J1234D/ByteBoard/assets/Renderings/untitled.199.jpg

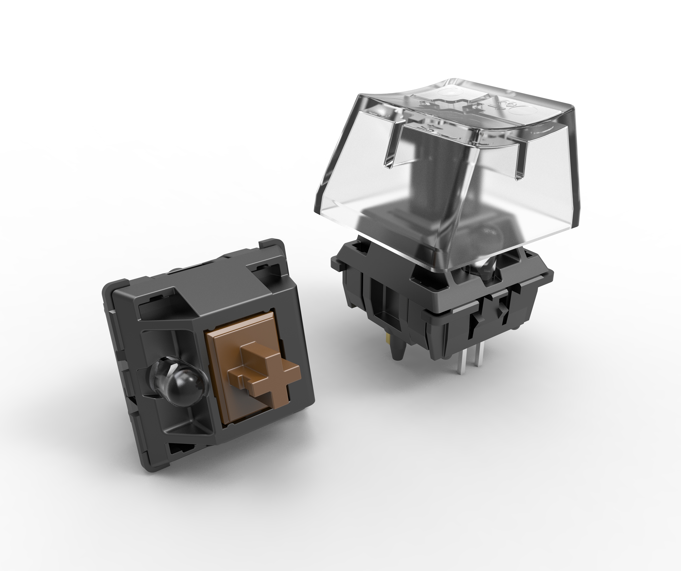
assets/Renderings/untitled.199.jpg
