J1234D/ByteBoard/assets/Renderings/屏幕截图(22).jpg

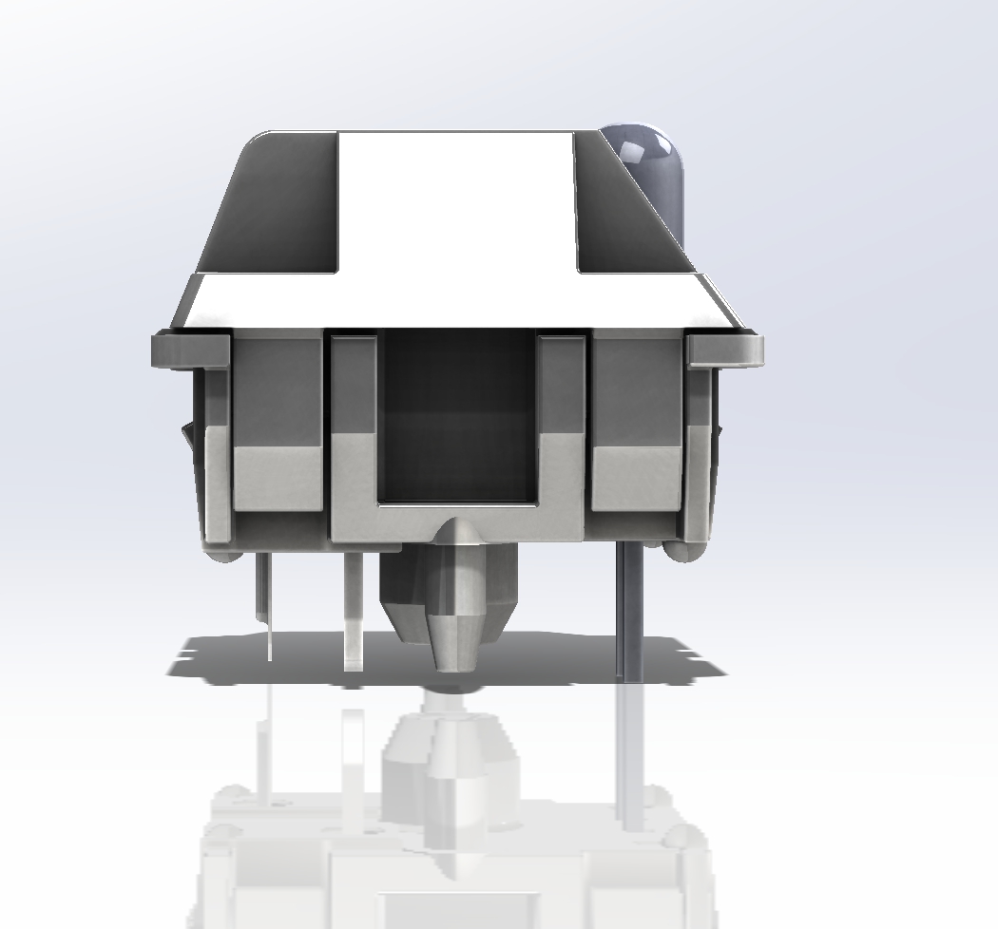
assets/Renderings/屏幕截图(22).jpg
