J1234D/ByteBoard/assets/Renderings/屏幕截图(25).jpg

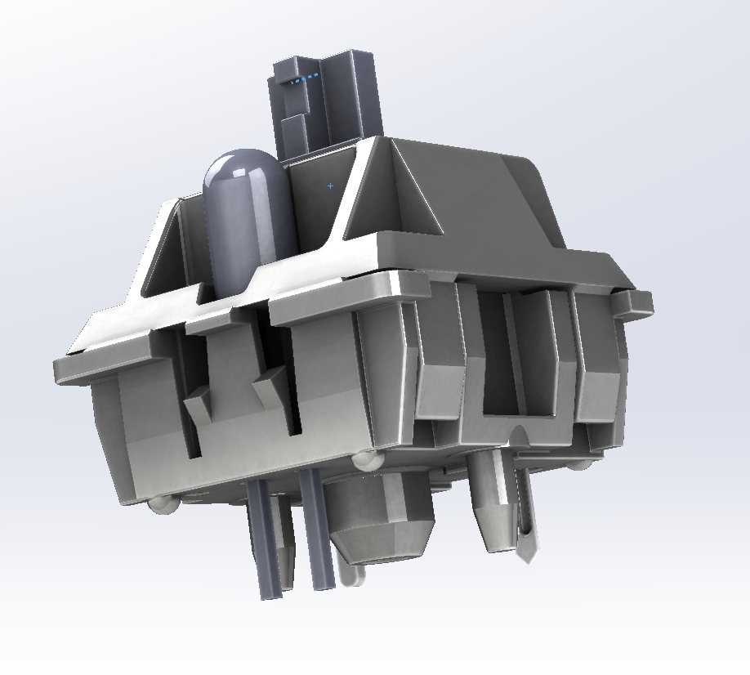
assets/Renderings/屏幕截图(25).jpg
