J1234D/ByteBoard/assets/Renderings/屏幕截图(26).jpg

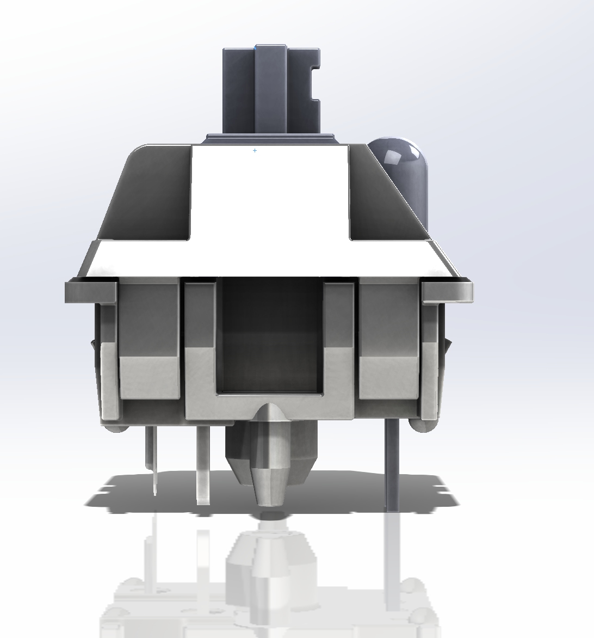
assets/Renderings/屏幕截图(26).jpg
