J1234D/ByteBoard/assets/Renderings/屏幕截图(27)_副本.jpg

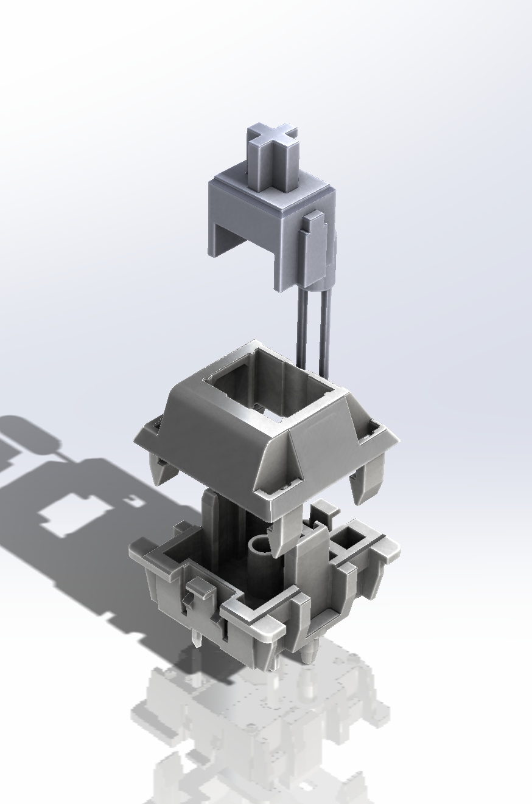
assets/Renderings/屏幕截图(27)_副本.jpg
