J1234D/ByteBoard/assets/Rotary_encoder/1.PNG

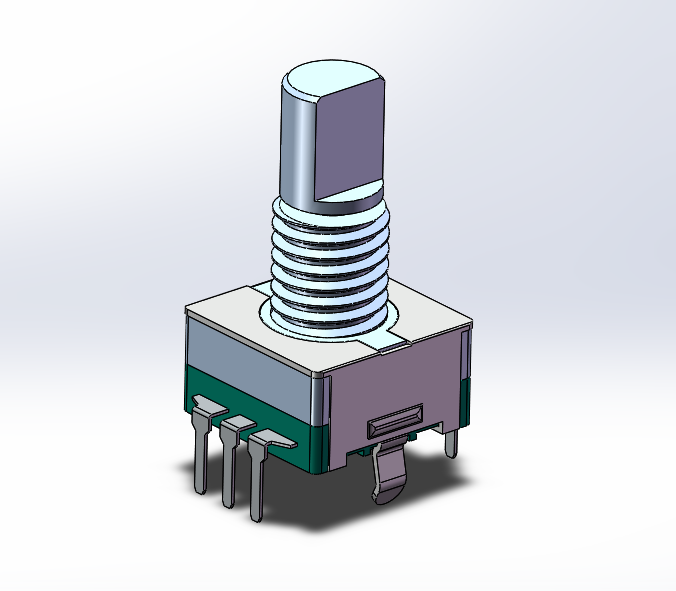
assets/Rotary_encoder/1.PNG
