J1234D/ByteBoard/assets/Rotary_encoder/2.PNG

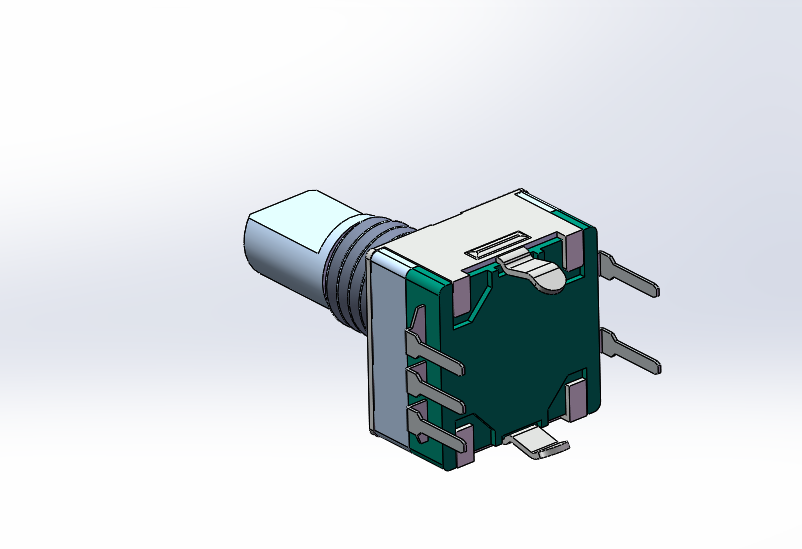
assets/Rotary_encoder/2.PNG
