J1234D/ByteBoard/assets/CherryMX-master/r4 legended/STP/275/Shift icon and text.stp

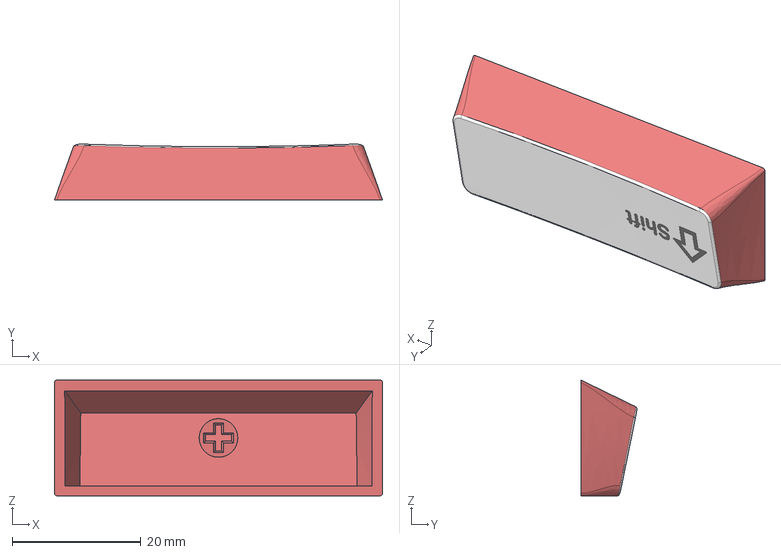
[picture p24: CAD file, 2026-06-21]
assets/CherryMX-master/r4 legended/STP/275/Shift icon and text.stp
51.0 x 8.68 x 18.0 mm
