J1234D/ByteBoard/assets/CherryMX-master/r4 legended/STP/2up/Enter text.stp

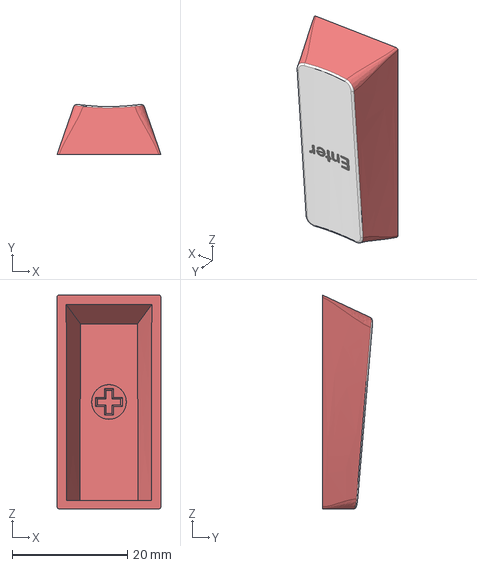
[picture p25: CAD file, 2026-06-21]
assets/CherryMX-master/r4 legended/STP/2up/Enter text.stp
18.0 x 8.64 x 37.1 mm
