J1234D/ByteBoard/assets/CherryMX-master/SLDPRT/spacebars/r4_625.SLDPRT

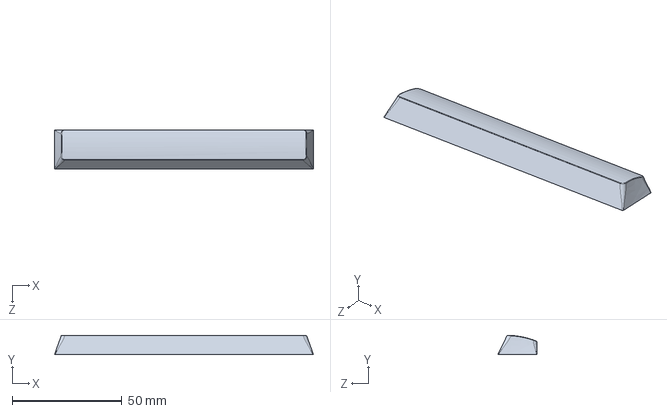
[picture p26: CAD file, 2026-06-21]
assets/CherryMX-master/SLDPRT/spacebars/r4_625.SLDPRT
118.1 x 8.80 x 18.0 mm
