J1234D/ByteBoard/assets/CherryMX-master/STEP/r2/r2_100.STEP

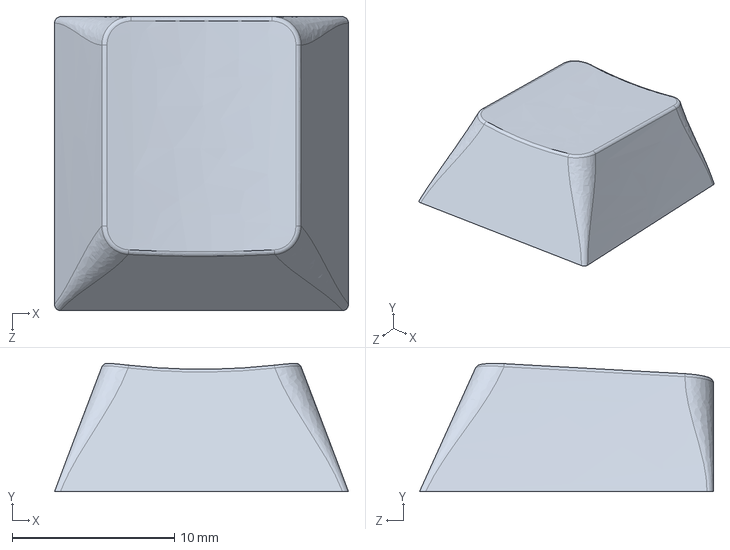
[picture p27: CAD file, 2026-06-21]
assets/CherryMX-master/STEP/r2/r2_100.STEP
18.1 x 7.89 x 18.1 mm
