J1234D/ByteBoard/assets/CherryMX-master/STEP/r3/r3_100.STEP

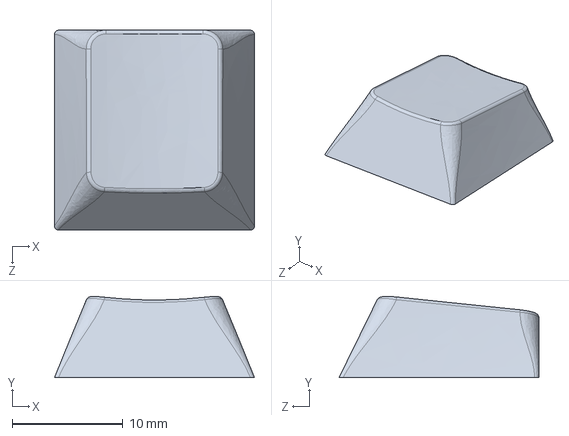
[picture p28: CAD file, 2026-06-21]
assets/CherryMX-master/STEP/r3/r3_100.STEP
18.1 x 7.34 x 18.1 mm
