J1234D/ByteBoard/assets/MX_switches/MX .STEP

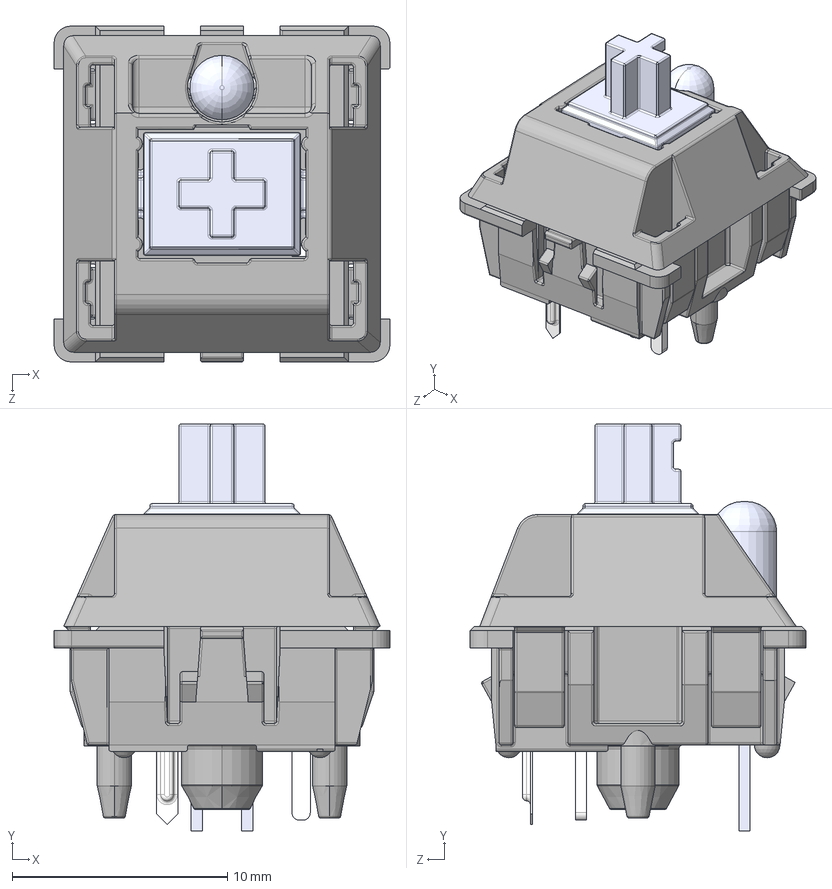
[picture p30: CAD file, 2026-06-21]
assets/MX_switches/MX .STEP
15.6 x 18.9 x 15.6 mm
MX 轴 按键′_ü___¨1
MX 轴 轴体áì_¨￠¨__
MX粣 拸簽LEDLEDLED
MX轴 轴体 底部 μ×2__默认_á2____è_
针脚___默认__è_
