J1234D/ByteBoard/assets/Rotary_encoder/rotaryencoder.STEP

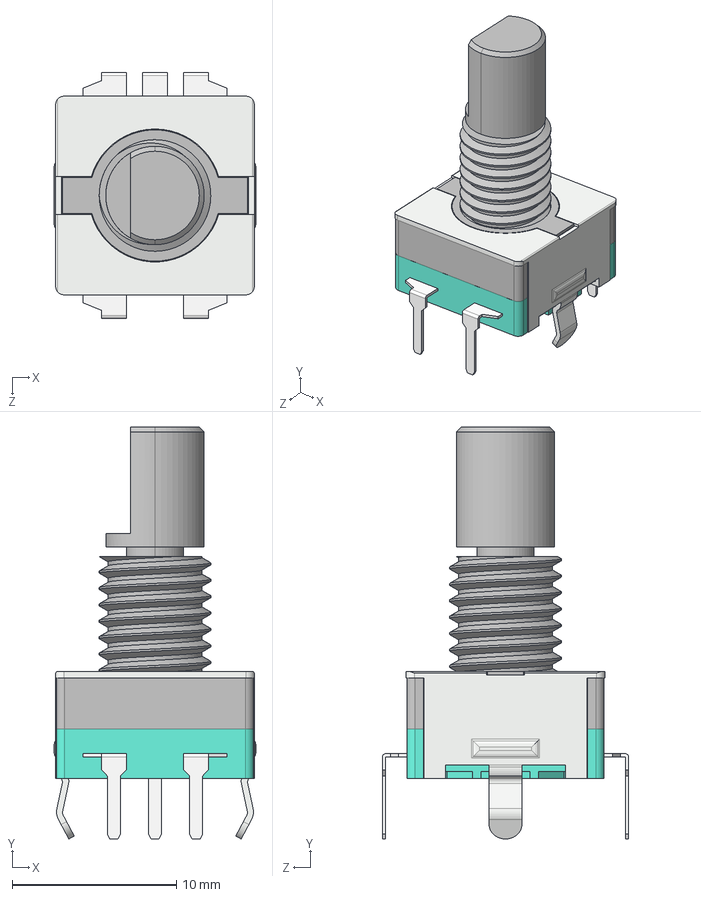
[picture p32: CAD file, 2026-06-21]
assets/Rotary_encoder/rotaryencoder.STEP
12.3 x 25.1 x 15.0 mm
