J1234D/ByteBoard/CAD/Top_Case.step

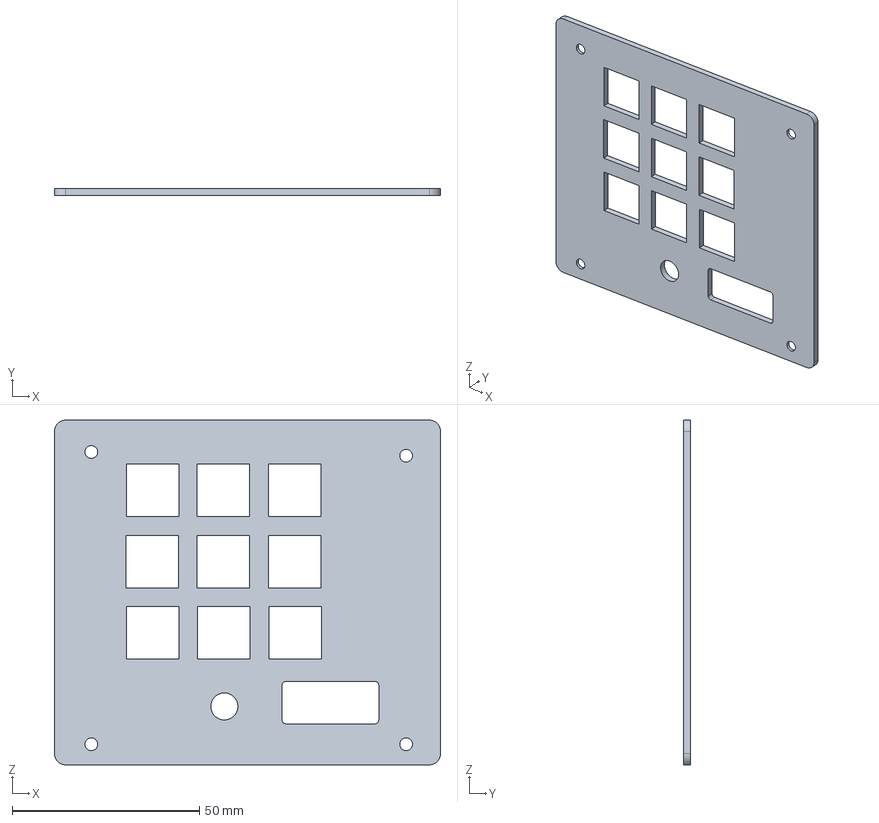
[picture p33: CAD file, 2026-06-28]
CAD/Top_Case.step
103.0 x 2.00 x 92.0 mm
