J1234D/ByteBoard/assets/CherryMX-master/r3 legended/STP/175/Caps Lock icon.stp

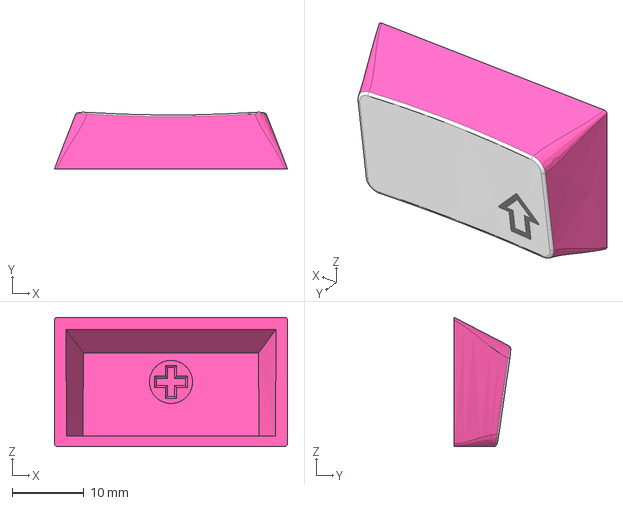
[picture p34: CAD file, 2026-06-21]
assets/CherryMX-master/r3 legended/STP/175/Caps Lock icon.stp
32.4 x 7.87 x 18.0 mm
