J1234D/ByteBoard/assets/CherryMX-master/SLDPRT/spacebars/r4_600.SLDPRT

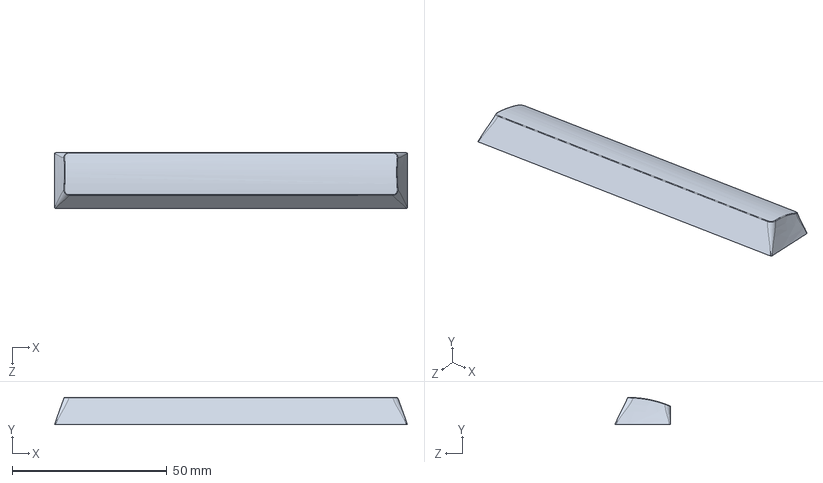
[picture p35: CAD file, 2026-06-21]
assets/CherryMX-master/SLDPRT/spacebars/r4_600.SLDPRT
114.0 x 8.80 x 18.0 mm
