J1234D/ByteBoard/assets/CherryMX-master/STEP/r2/r2_150.STEP

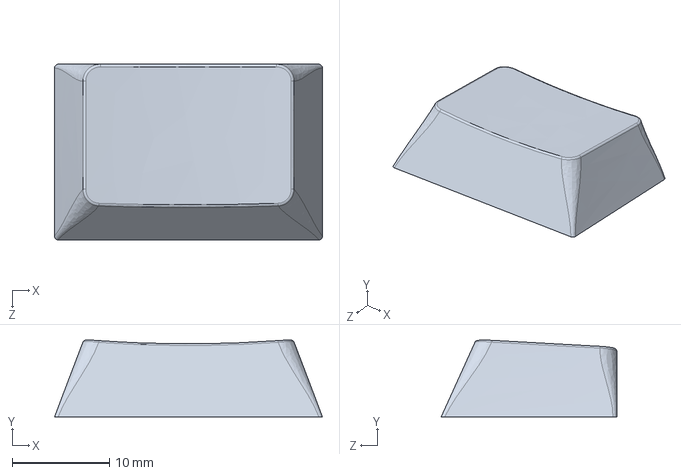
[picture p36: CAD file, 2026-06-21]
assets/CherryMX-master/STEP/r2/r2_150.STEP
27.6 x 7.92 x 18.1 mm
