J1234D/ByteBoard/assets/CherryMX-master/STEP/r3/r2-3_200vert.STEP

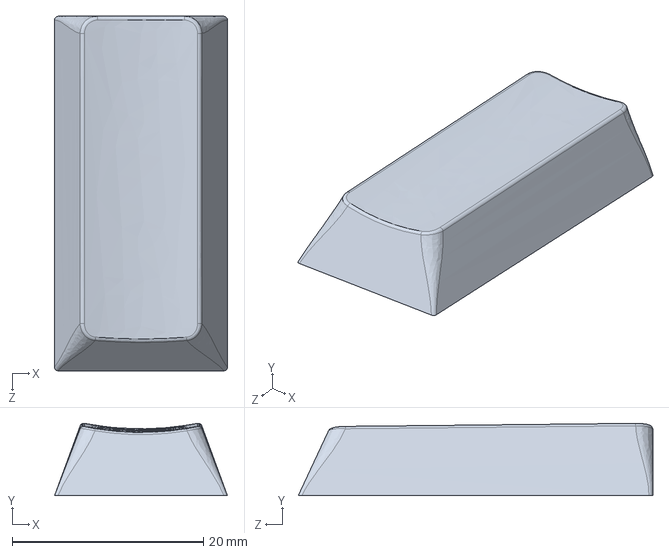
[picture p37: CAD file, 2026-06-21]
assets/CherryMX-master/STEP/r3/r2-3_200vert.STEP
18.1 x 7.57 x 37.1 mm
