J1234D/ByteBoard/assets/CherryMX-master/STEP/r4/r4_300C.step

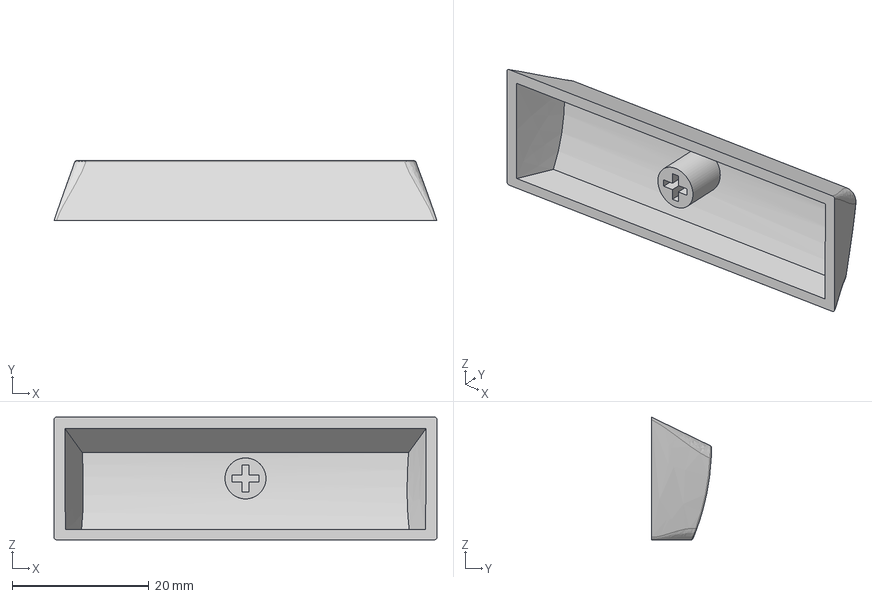
[picture p38: CAD file, 2026-06-21]
assets/CherryMX-master/STEP/r4/r4_300C.step
56.1 x 8.80 x 18.0 mm
