J1234D/ByteBoard/CAD/Bottom_Case.step

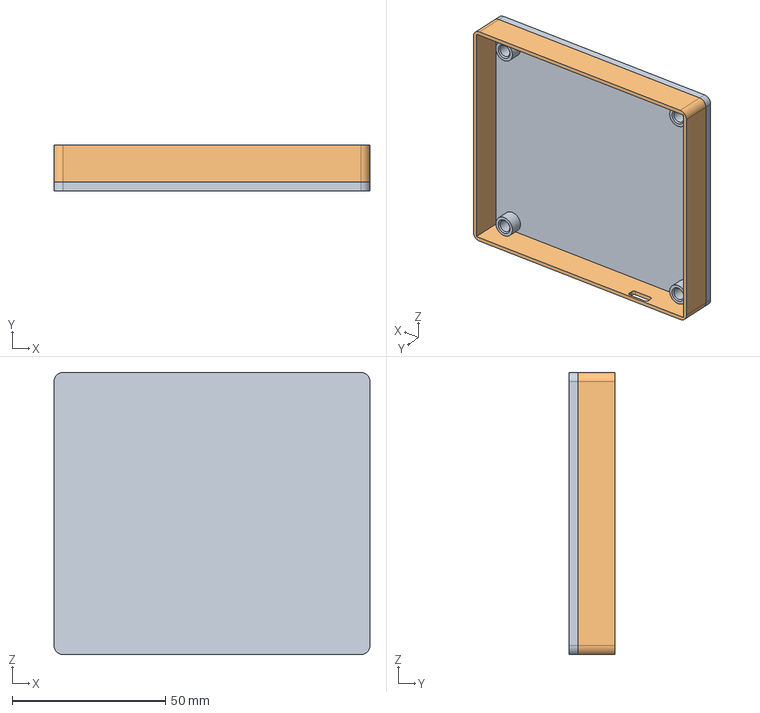
[picture p39: CAD file, 2026-06-28]
CAD/Bottom_Case.step
103.0 x 15.0 x 92.0 mm
