J1234D/ByteBoard/assets/CherryMX-master/r4 legended/STP/125/Shift icon and text.stp

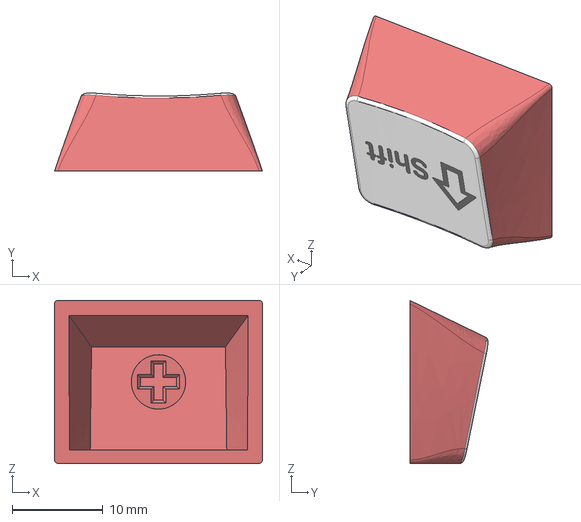
[picture p40: CAD file, 2026-06-21]
assets/CherryMX-master/r4 legended/STP/125/Shift icon and text.stp
22.9 x 8.61 x 18.0 mm
