J1234D/ByteBoard/assets/CherryMX-master/SLDPRT/spacebars/r4_700.SLDPRT

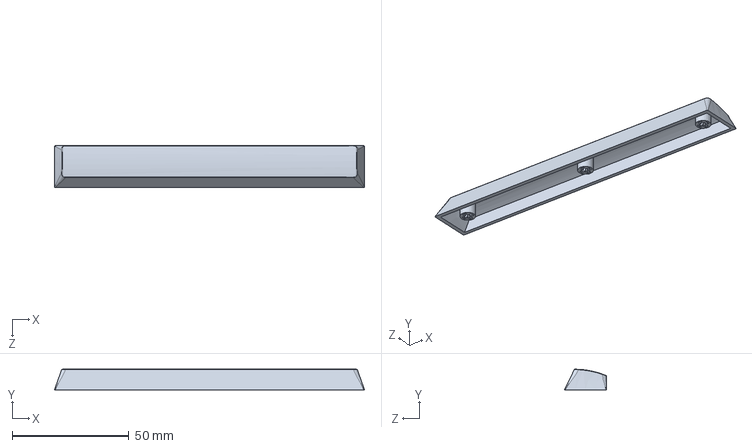
[picture p41: CAD file, 2026-06-21]
assets/CherryMX-master/SLDPRT/spacebars/r4_700.SLDPRT
132.5 x 8.80 x 18.0 mm
