J1234D/ByteBoard/assets/CherryMX-master/STEP/r3/r3_125.STEP

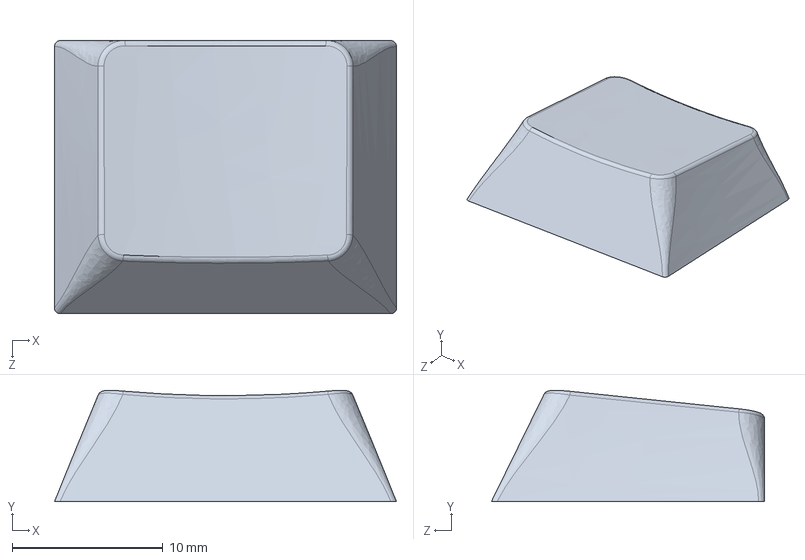
[picture p42: CAD file, 2026-06-21]
assets/CherryMX-master/STEP/r3/r3_125.STEP
22.7 x 7.36 x 18.1 mm
