J1234D/ByteBoard/assets/CherryMX-master/STEP/r4/r3-4_200vert.STEP

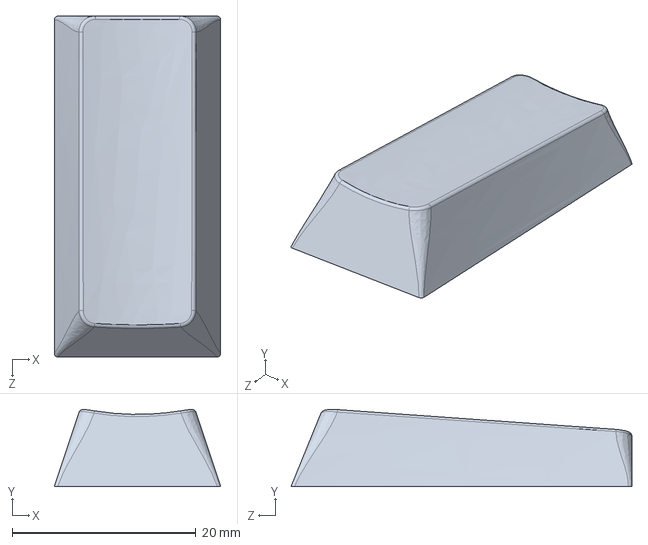
[picture p43: CAD file, 2026-06-21]
assets/CherryMX-master/STEP/r4/r3-4_200vert.STEP
18.1 x 8.38 x 37.1 mm
