J1234D/ByteBoard/assets/CherryMX-master/STEP/r4/r4_175.STEP

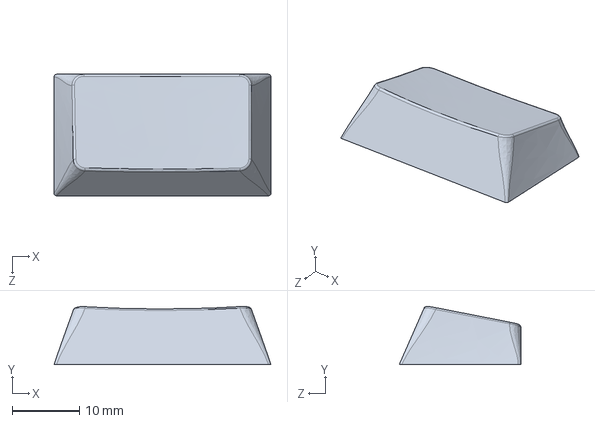
[picture p44: CAD file, 2026-06-21]
assets/CherryMX-master/STEP/r4/r4_175.STEP
32.3 x 8.65 x 18.1 mm
