J1234D/ByteBoard/assets/CherryMX-master/STEP/r3/r3_200.STEP

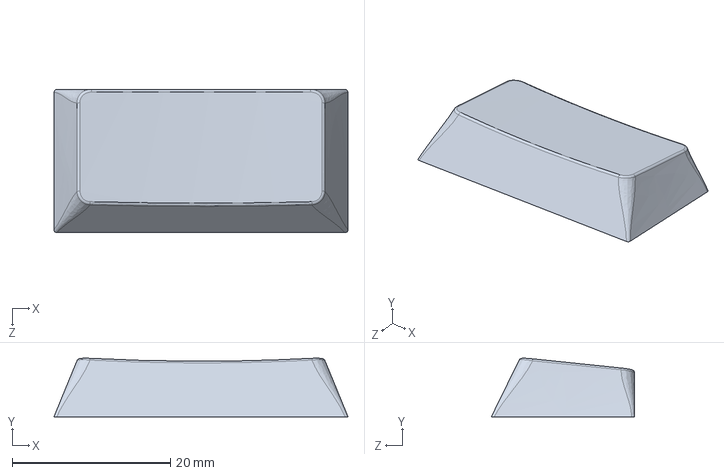
[picture p45: CAD file, 2026-06-21]
assets/CherryMX-master/STEP/r3/r3_200.STEP
37.1 x 7.40 x 18.1 mm
