J1234D/ByteBoard/assets/CherryMX-master/STEP/r4/r4_225.STEP

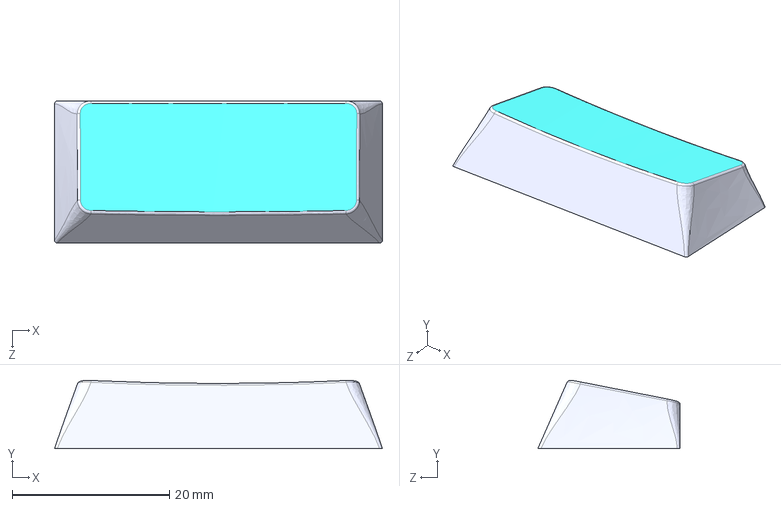
[picture p46: CAD file, 2026-06-21]
assets/CherryMX-master/STEP/r4/r4_225.STEP
41.7 x 8.67 x 18.1 mm
