J1234D/ByteBoard/assets/CherryMX-master/STEP/r3/r3_100_sculpted.STEP

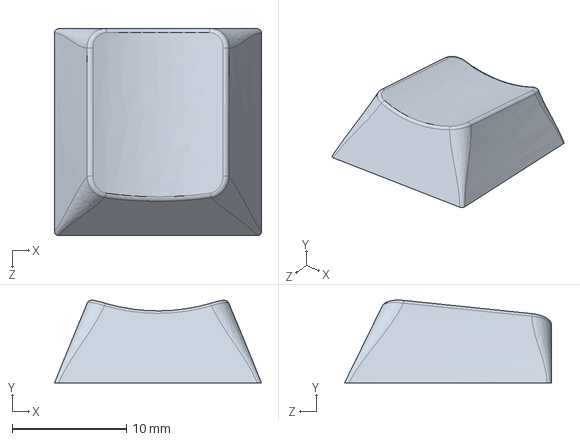
[picture p47: CAD file, 2026-06-21]
assets/CherryMX-master/STEP/r3/r3_100_sculpted.STEP
18.1 x 7.24 x 18.1 mm
