J1234D/ByteBoard/assets/CherryMX-master/STEP/r4/r4_225C.step

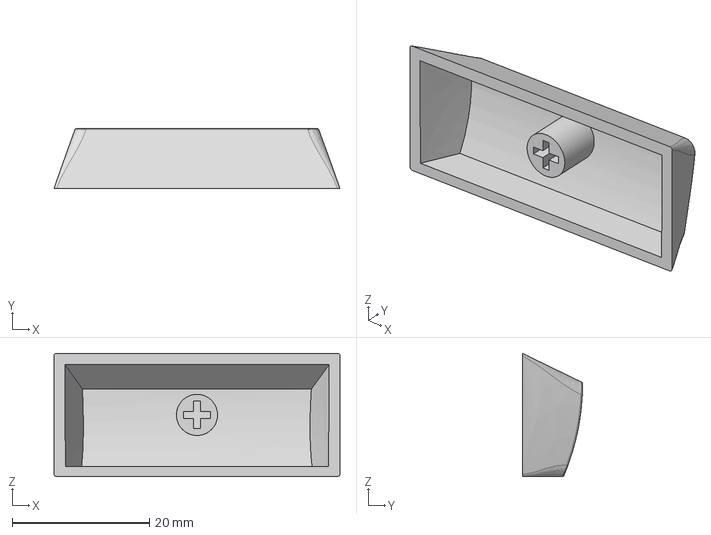
[picture p48: CAD file, 2026-06-21]
assets/CherryMX-master/STEP/r4/r4_225C.step
41.7 x 8.80 x 18.0 mm
