J1234D/ByteBoard/assets/CherryMX-master/r1 legended/STP/F2.stp

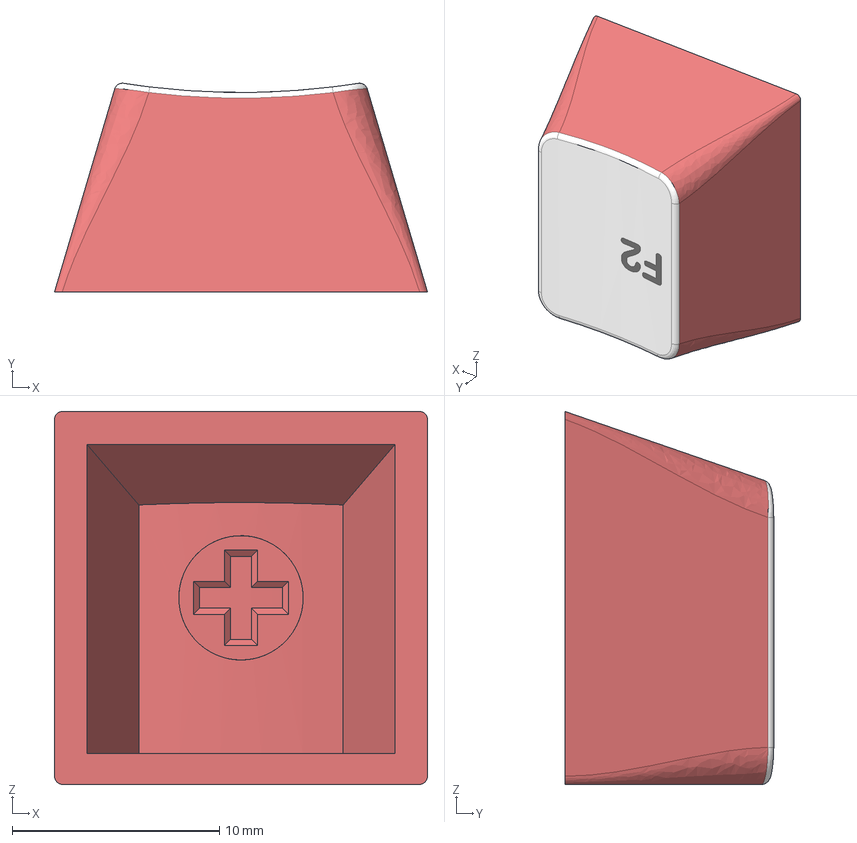
[picture p49: CAD file, 2026-06-21]
assets/CherryMX-master/r1 legended/STP/F2.stp
18.0 x 10.1 x 18.0 mm
