J1234D/ByteBoard/assets/CherryMX-master/STEP/r3/r3_175.STEP

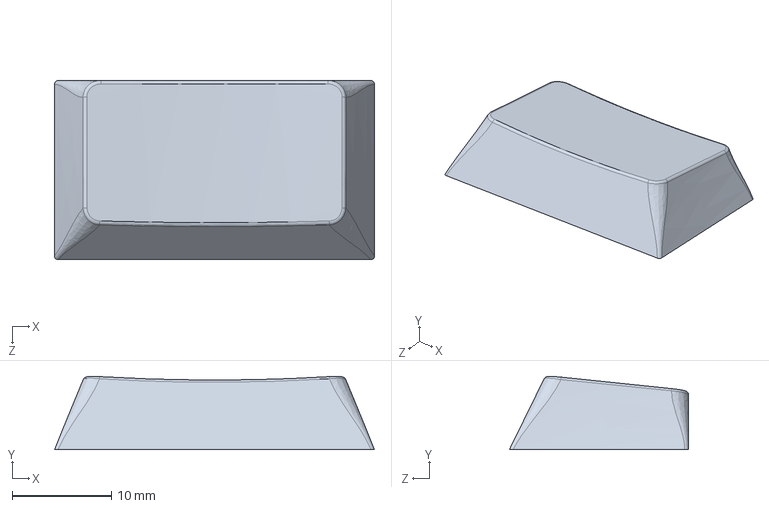
[picture p50: CAD file, 2026-06-21]
assets/CherryMX-master/STEP/r3/r3_175.STEP
32.3 x 7.39 x 18.1 mm
