J1234D/ByteBoard/assets/CherryMX-master/STEP/r3/r3_iso.STEP

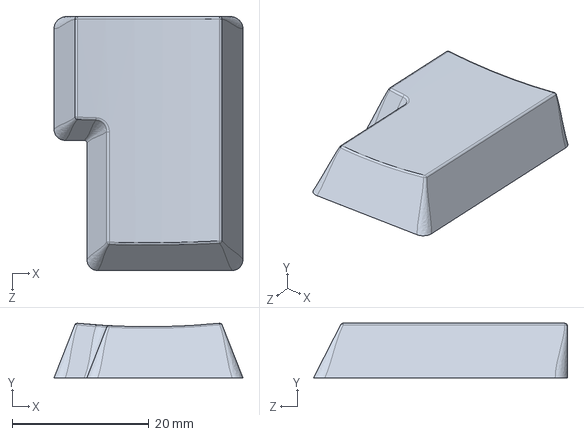
[picture p51: CAD file, 2026-06-21]
assets/CherryMX-master/STEP/r3/r3_iso.STEP
27.6 x 7.97 x 37.1 mm
