J1234D/ByteBoard/assets/CherryMX-master/STEP/r4/r4_200.STEP

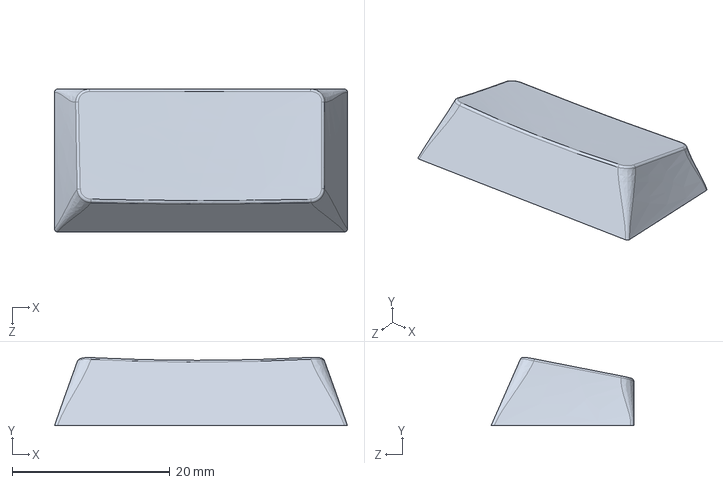
[picture p52: CAD file, 2026-06-21]
assets/CherryMX-master/STEP/r4/r4_200.STEP
37.1 x 8.66 x 18.1 mm
