J1234D/ByteBoard/assets/CherryMX-master/STEP/r3/r3_225.STEP

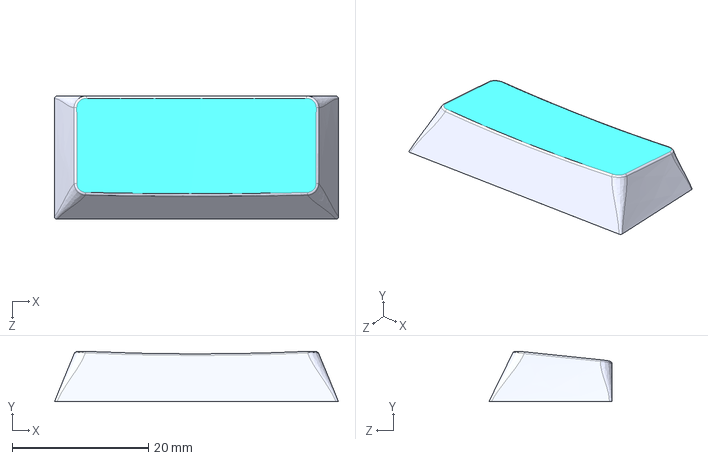
[picture p53: CAD file, 2026-06-21]
assets/CherryMX-master/STEP/r3/r3_225.STEP
41.7 x 7.41 x 18.1 mm
