J1234D/ByteBoard/assets/CherryMX-master/STEP/r3/r3_150.STEP

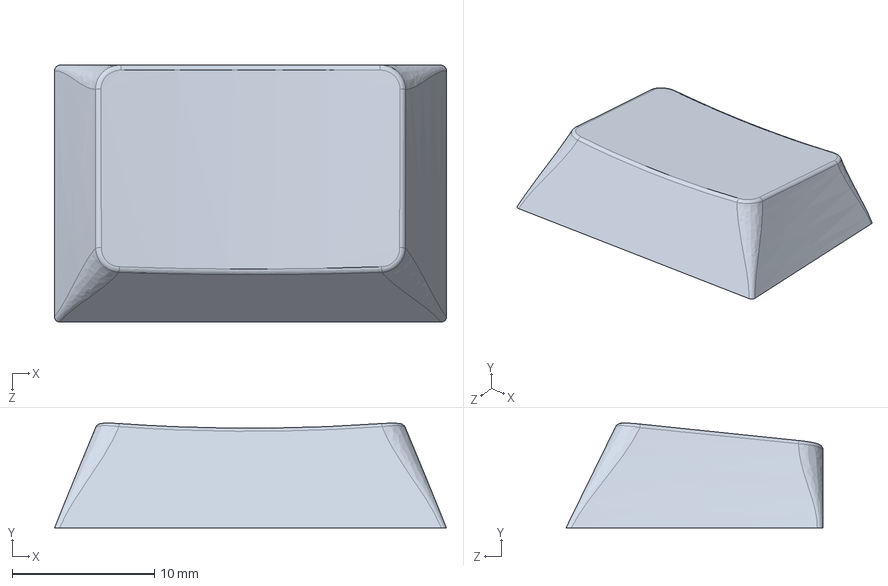
[picture p54: CAD file, 2026-06-21]
assets/CherryMX-master/STEP/r3/r3_150.STEP
27.6 x 7.38 x 18.1 mm
