J1234D/ByteBoard/assets/CherryMX-master/STEP/r4/r4_275.STEP

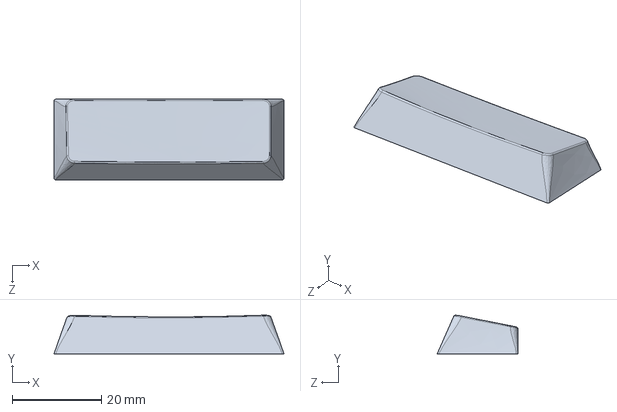
[picture p55: CAD file, 2026-06-21]
assets/CherryMX-master/STEP/r4/r4_275.STEP
51.6 x 8.69 x 18.1 mm
